hannobraun/notebooks/documentation/tools/hole-guide/export/top.scad

use <../modules.scad>

top();
