hannobraun/notebooks/work-log/2022-05-04.jpg

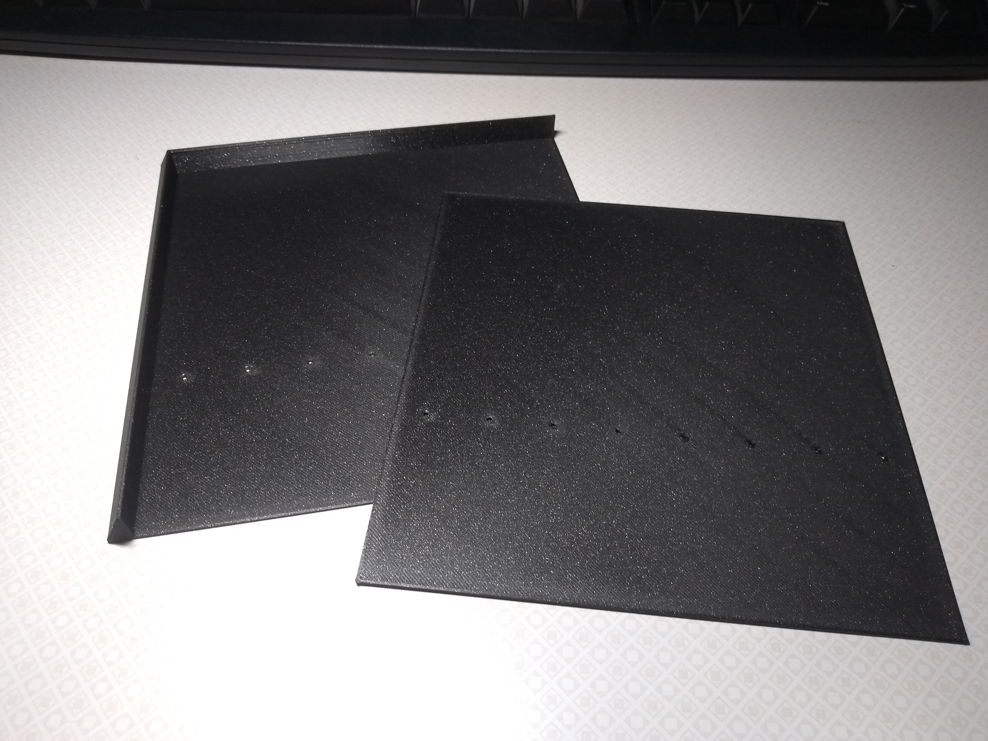
work-log/2022-05-04.jpg
